soranaulm/InkTime-proiect-tsc/Images/Screenshot 2026-04-10 162956.png

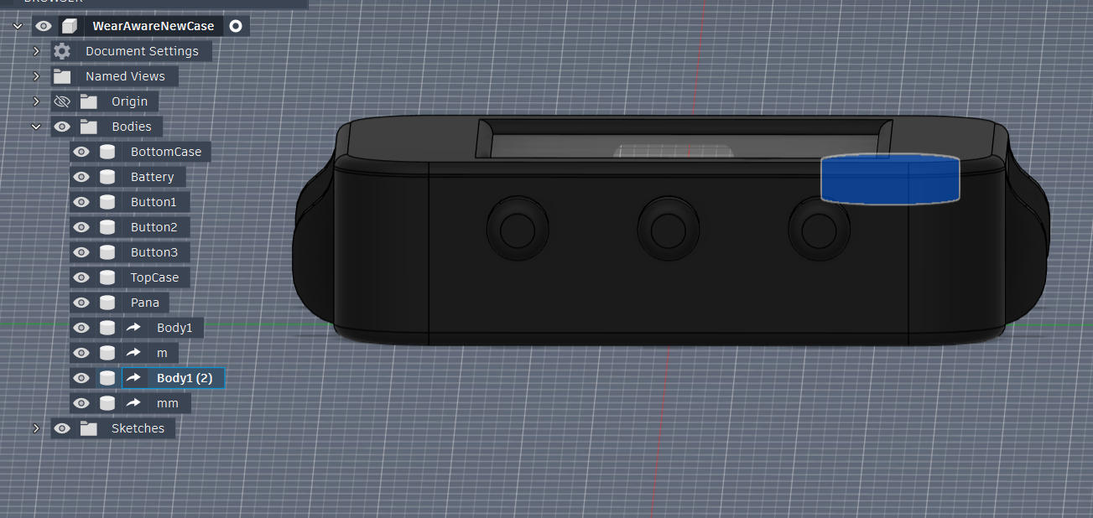
Images/Screenshot 2026-04-10 162956.png
