soranaulm/InkTime-proiect-tsc/Images/Screenshot 2026-04-21 114428.png

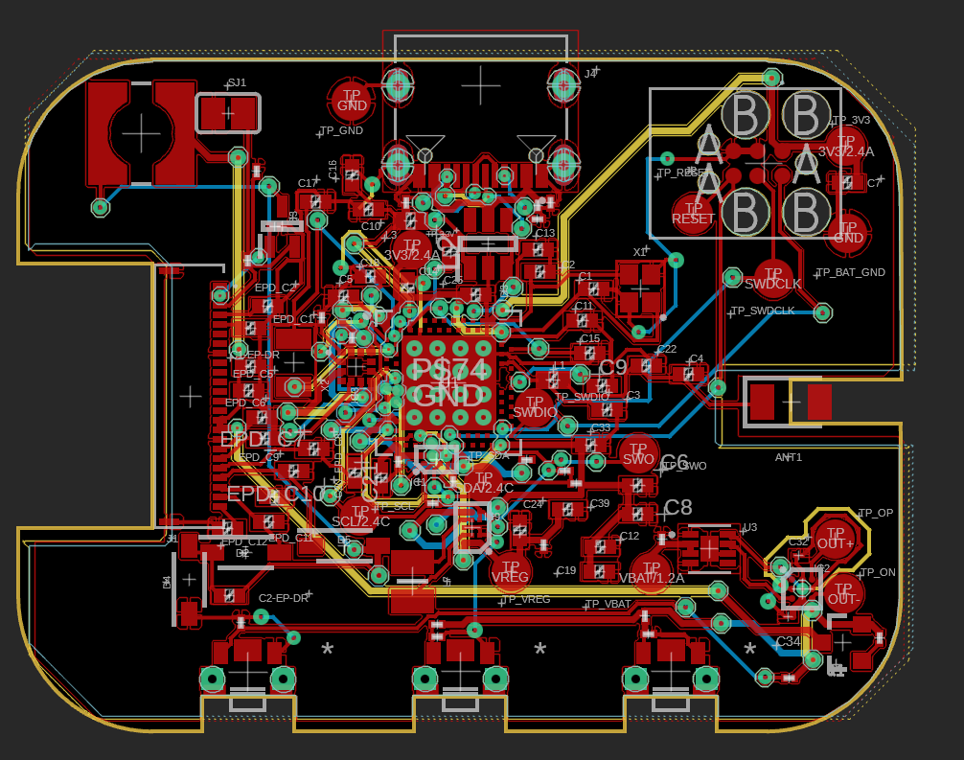
Images/Screenshot 2026-04-21 114428.png
